Jed0vcela/LabSupply-2025-2026/3D files/button handle tapered hole V2 NO_AMS.SLDPRT

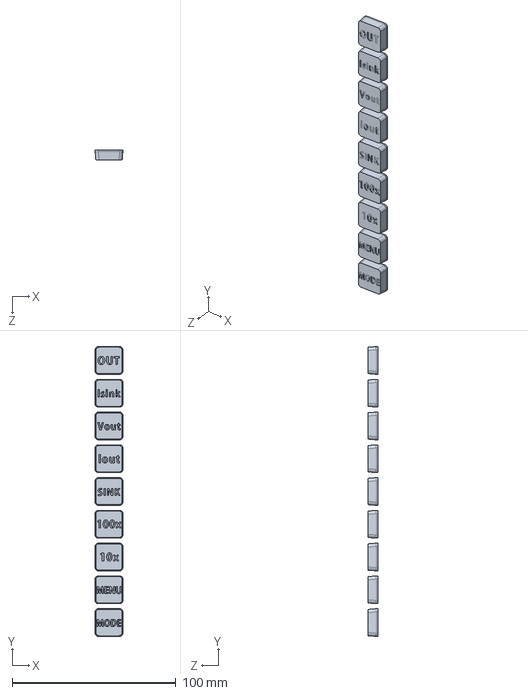
[picture p5: CAD file, 2026-05-19]
3D files/button handle tapered hole V2 NO_AMS.SLDPRT
17.0 x 177.0 x 6.00 mm
