Jed0vcela/LabSupply-2025-2026/3D files/STLs/button handle v2.STL

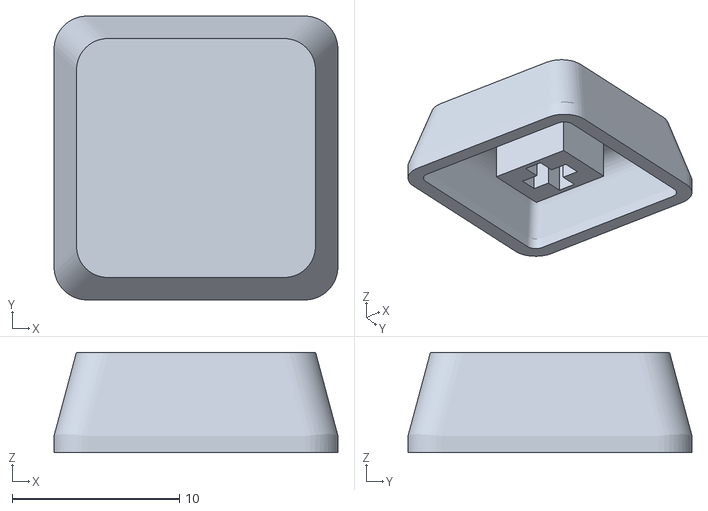
[picture p7: CAD file, 2026-05-17]
3D files/STLs/button handle v2.STL
17.0 x 17.0 x 6.00
