Jed0vcela/LabSupply-2025-2026/3D files/button handle tapered hole V2 AMS.SLDPRT

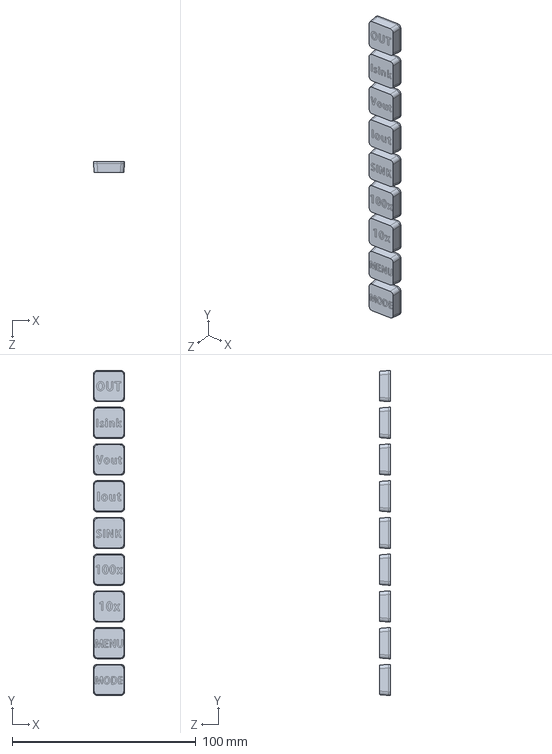
[picture p8: CAD file, 2026-05-18]
3D files/button handle tapered hole V2 AMS.SLDPRT
17.0 x 177.0 x 6.00 mm
