Jed0vcela/LabSupply-2025-2026/3D files/DXFc/FrontPanel1.DXF

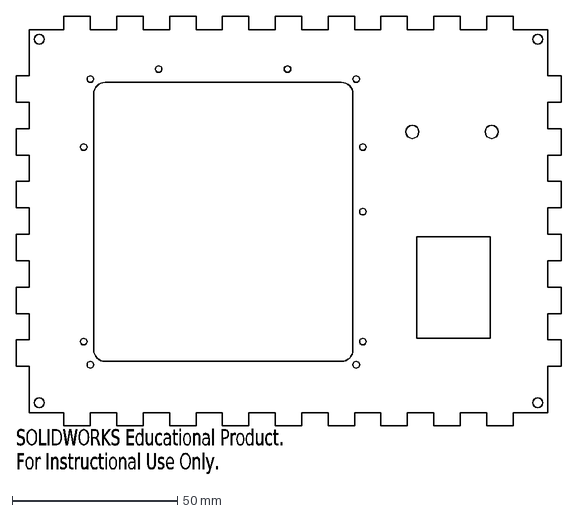
[picture p9: CAD file, 2026-05-18]
3D files/DXFc/FrontPanel1.DXF
SOLIDWORKS Educational Product.
For Instructional Use Only.
