Jed0vcela/LabSupply-2025-2026/3D files/STLs/front panel cover^supply_assem.STL

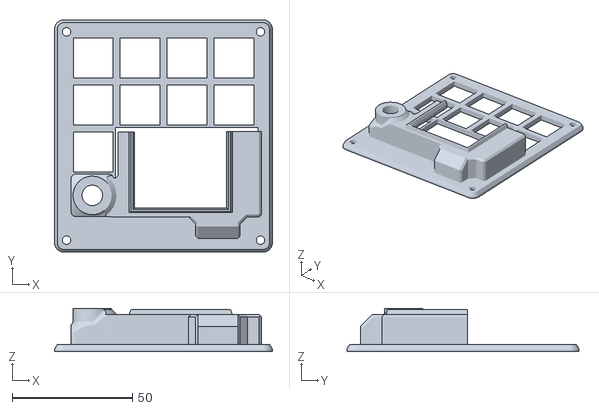
[picture p10: CAD file, 2026-05-17]
3D files/STLs/front panel cover^supply_assem.STL
90.5 x 96.5 x 18.0
