Jed0vcela/LabSupply-2025-2026/3D files/DXFc/RightPanel1.DXF

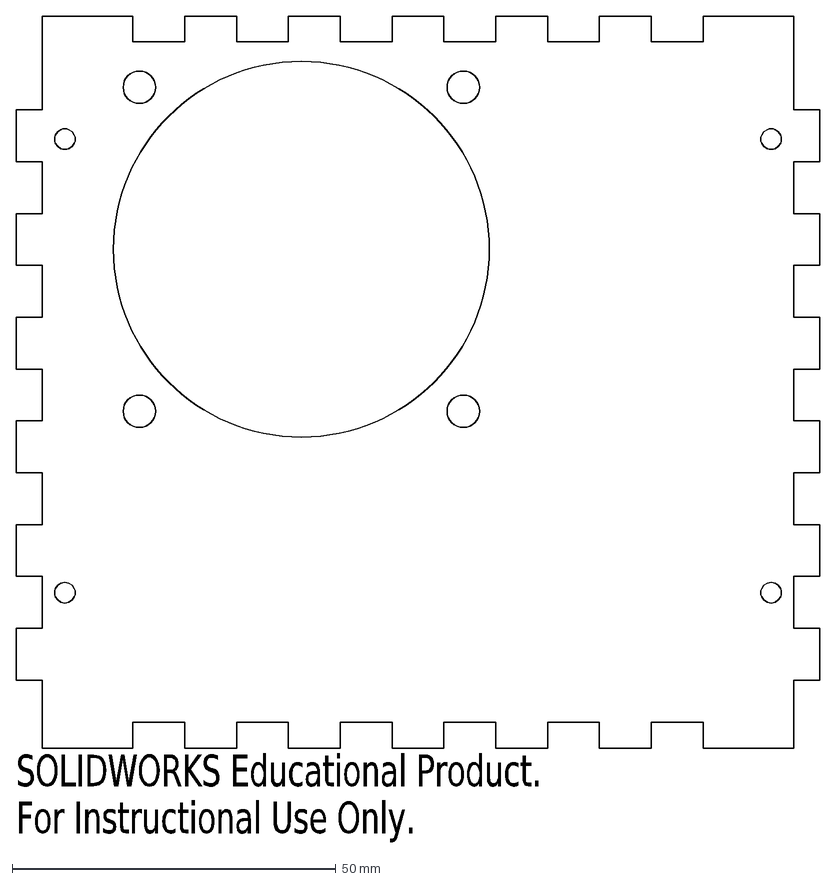
[picture p11: CAD file, 2026-05-18]
3D files/DXFc/RightPanel1.DXF
SOLIDWORKS Educational Product.
For Instructional Use Only.
