Jed0vcela/LabSupply-2025-2026/3D files/FrontPanel1.SLDPRT

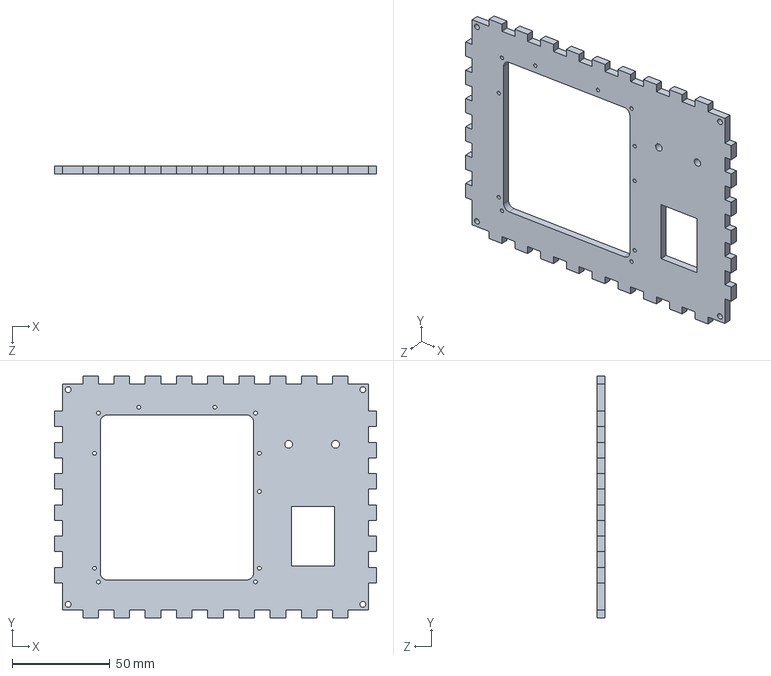
[picture p12: CAD file, 2026-05-18]
3D files/FrontPanel1.SLDPRT
165.0 x 124.0 x 4.00 mm
