Jed0vcela/LabSupply-2025-2026/3D files/PwrBrd/single-banana-jack-1.snapshot.2/Banana Jack/baseplate.SLDPRT

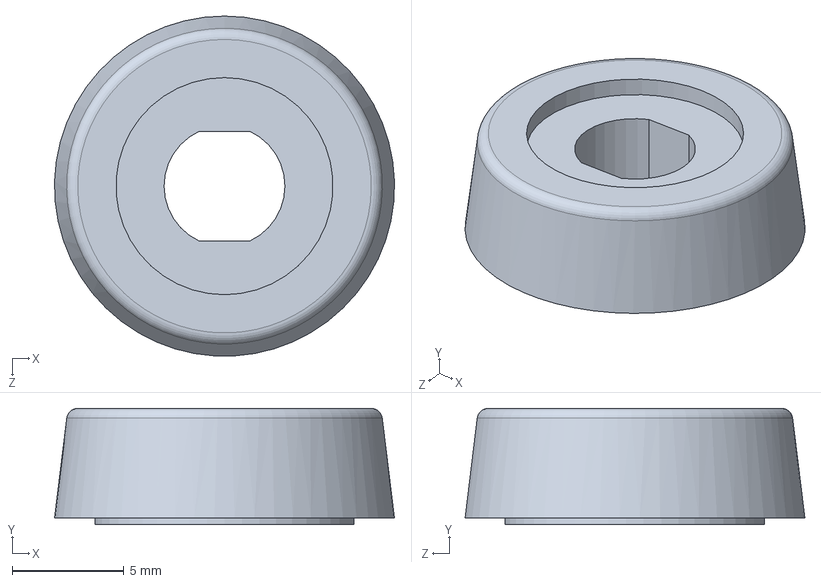
[picture p13: CAD file, 2026-05-11]
3D files/PwrBrd/single-banana-jack-1.snapshot.2/Banana Jack/baseplate.SLDPRT
15.2 x 5.20 x 15.2 mm
