Jed0vcela/LabSupply-2025-2026/3D files/STLs/front panel mount rear^supply_assem.STL

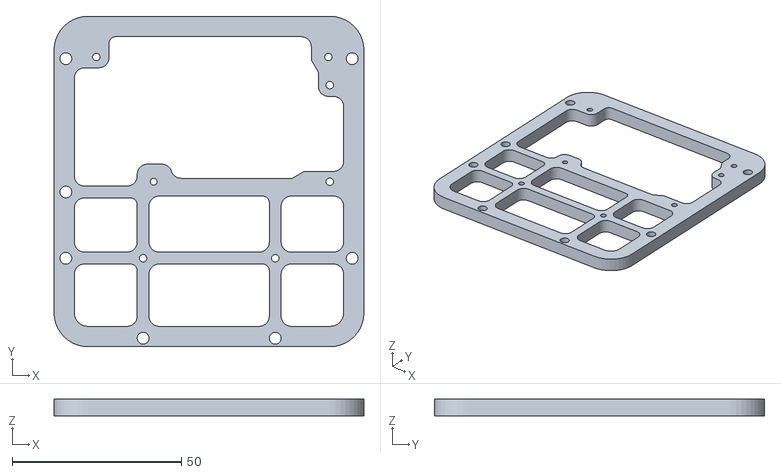
[picture p14: CAD file, 2026-05-16]
3D files/STLs/front panel mount rear^supply_assem.STL
91.5 x 97.5 x 5.00
