Jed0vcela/LabSupply-2025-2026/3D files/DXFc/Copy of TopPanel1^supply_assem.DXF

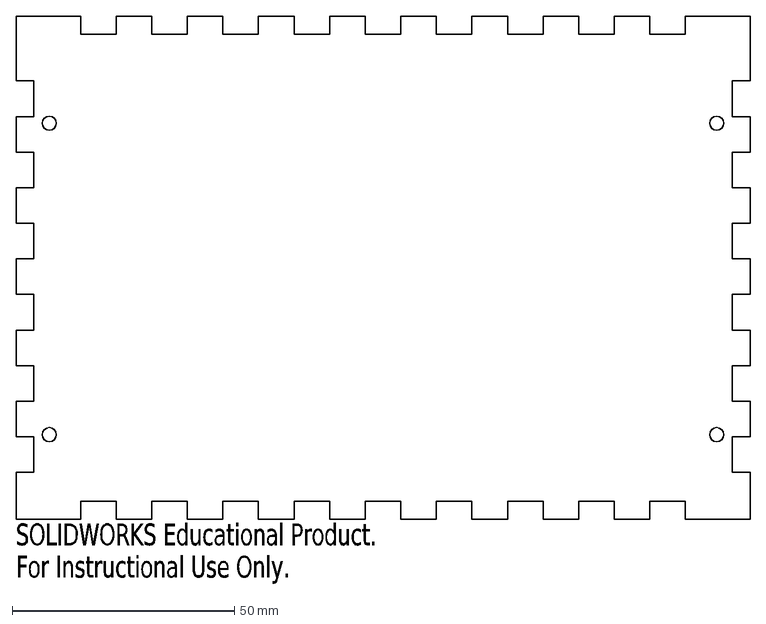
[picture p15: CAD file, 2026-05-18]
3D files/DXFc/Copy of TopPanel1^supply_assem.DXF
SOLIDWORKS Educational Product.
For Instructional Use Only.
