Jed0vcela/LabSupply-2025-2026/3D files/Fuse Holder 5x20mm v1.SLDPRT

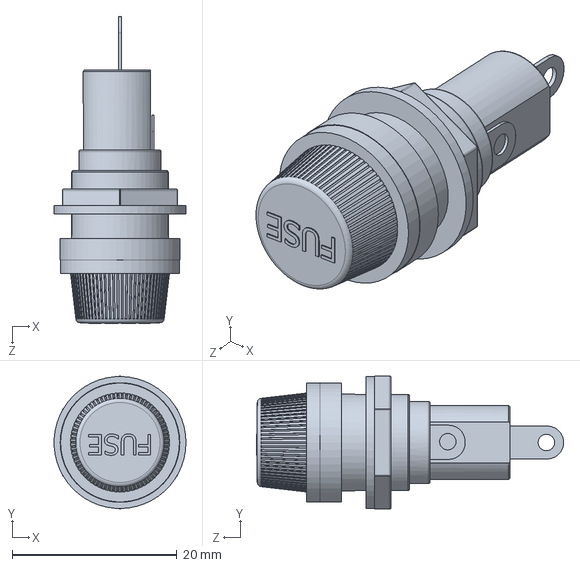
[picture p16: CAD file, 2026-05-18]
3D files/Fuse Holder 5x20mm v1.SLDPRT
16.0 x 16.1 x 37.2 mm
