Jed0vcela/LabSupply-2025-2026/3D files/STLs/drill guide^supply_assem.STL

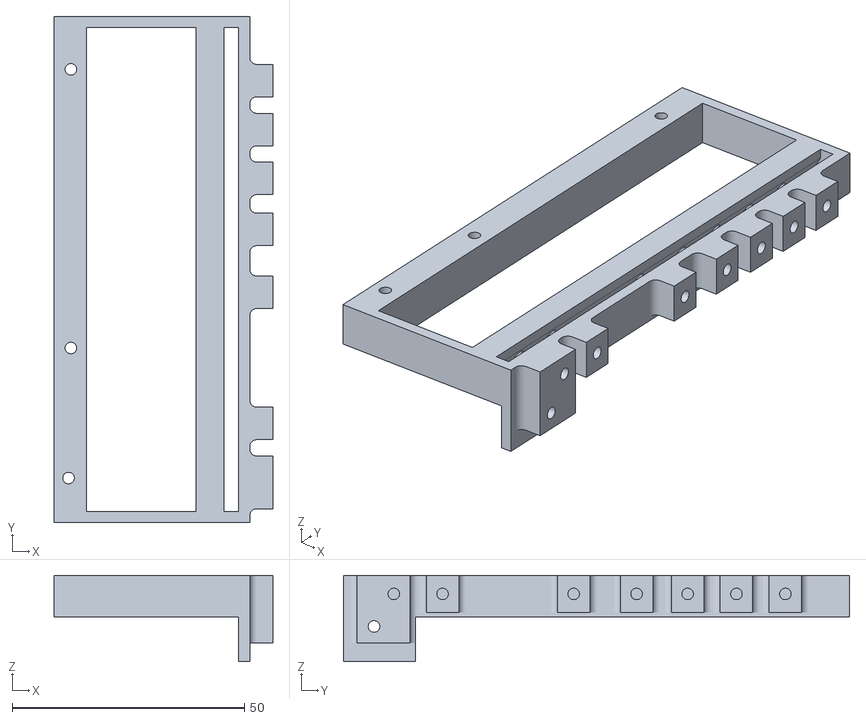
[picture p17: CAD file, 2026-05-11]
3D files/STLs/drill guide^supply_assem.STL
47.2 x 109.0 x 18.6
