Jed0vcela/LabSupply-2025-2026/3D files/STLs/USB-C PD trigger holder^supply_assem.STL

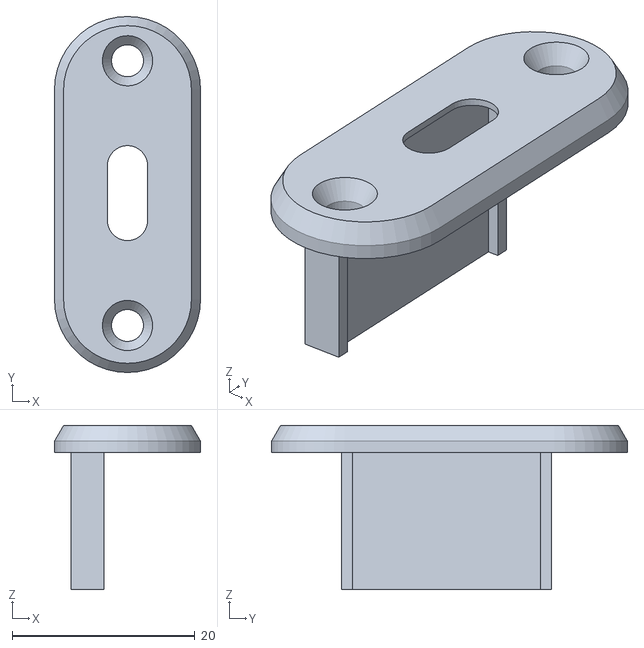
[picture p19: CAD file, 2026-05-11]
3D files/STLs/USB-C PD trigger holder^supply_assem.STL
16.0 x 39.0 x 18.0
