Jed0vcela/LabSupply-2025-2026/3D files/DXFc/BottomPanel1.DXF

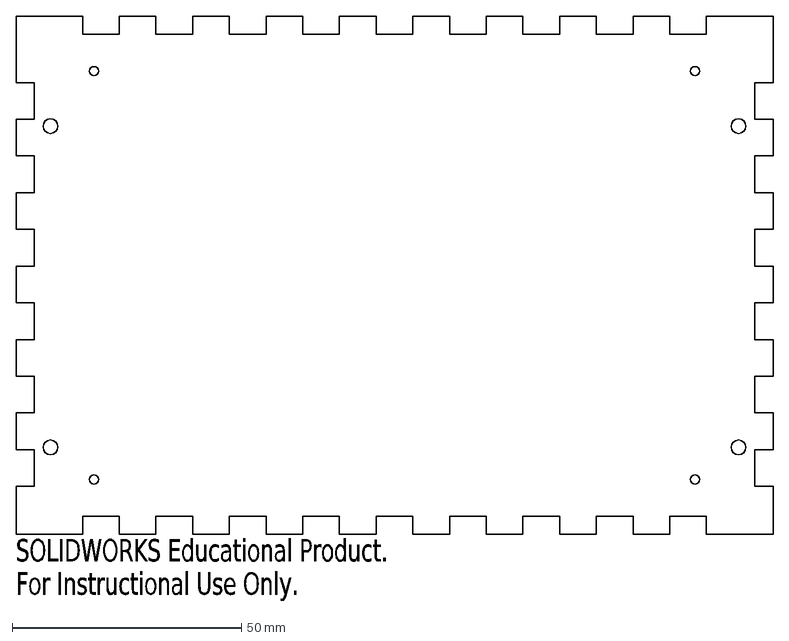
[picture p20: CAD file, 2026-05-18]
3D files/DXFc/BottomPanel1.DXF
SOLIDWORKS Educational Product.
For Instructional Use Only.
