Jed0vcela/LabSupply-2025-2026/3D files/knob1.SLDPRT

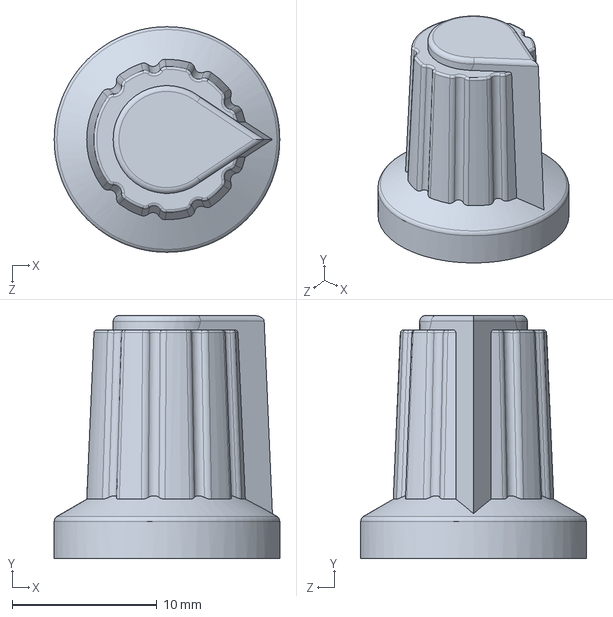
[picture p21: CAD file, 2026-05-18]
3D files/knob1.SLDPRT
15.6 x 16.8 x 15.6 mm
