Jed0vcela/LabSupply-2025-2026/3D files/STLs/fan side holder^supply_assem.STL

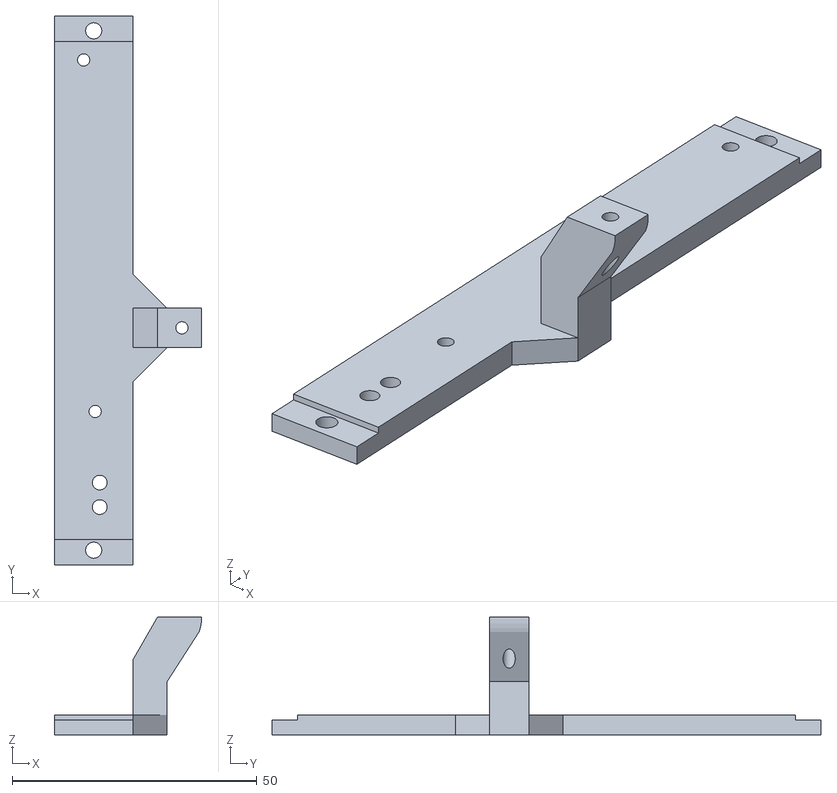
[picture p22: CAD file, 2026-05-11]
3D files/STLs/fan side holder^supply_assem.STL
30.0 x 112.0 x 24.0
