Jed0vcela/LabSupply-2025-2026/3D files/DXFc/frame^supply_assem.STL

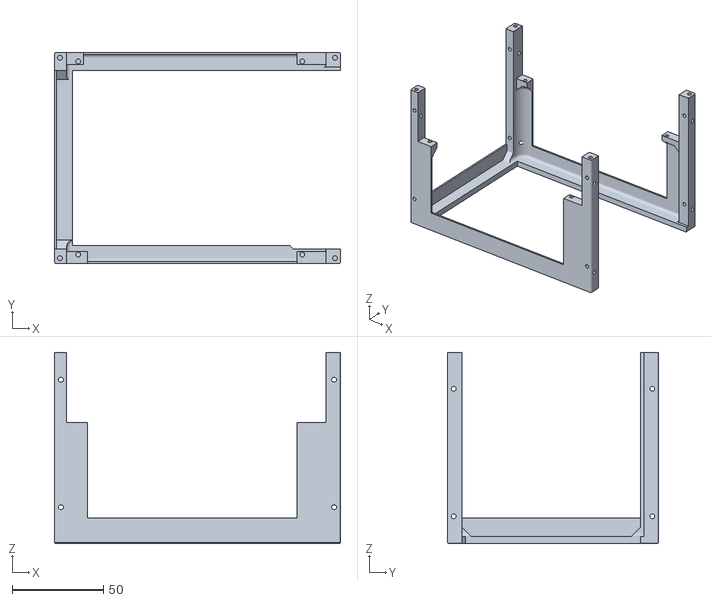
[picture p23: CAD file, 2026-05-11]
3D files/DXFc/frame^supply_assem.STL
157.0 x 116.0 x 105.0
