Jed0vcela/LabSupply-2025-2026/3D files/LeftPanel1.SLDPRT

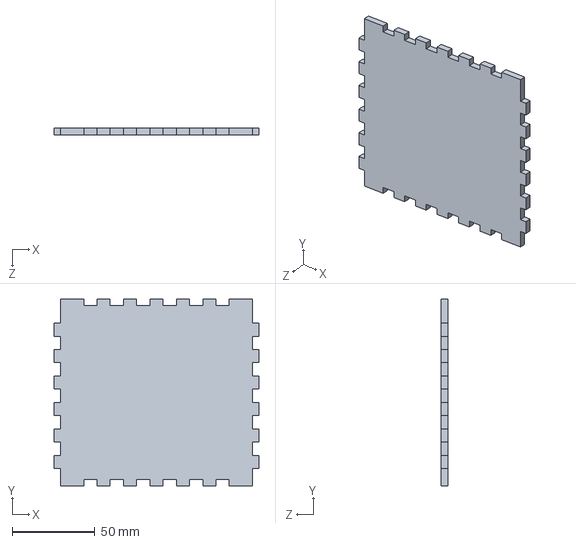
[picture p24: CAD file, 2026-05-18]
3D files/LeftPanel1.SLDPRT
124.0 x 113.0 x 4.00 mm
