Jed0vcela/LabSupply-2025-2026/3D files/PwrBrd/single-banana-jack-1.snapshot.2/Banana Jack/baseplate_1.SLDPRT

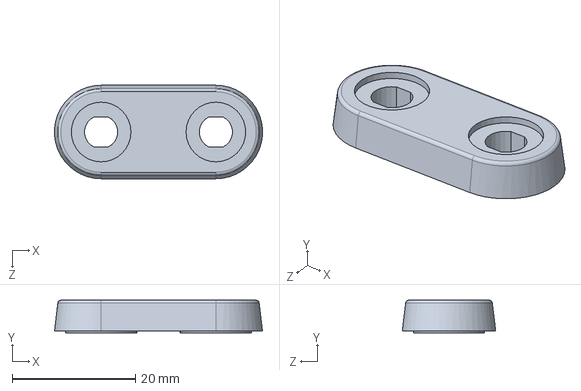
[picture p25: CAD file, 2026-05-11]
3D files/PwrBrd/single-banana-jack-1.snapshot.2/Banana Jack/baseplate_1.SLDPRT
33.8 x 5.30 x 15.2 mm
