Jed0vcela/LabSupply-2025-2026/3D files/STLs/USB cover^supply_assem.STL

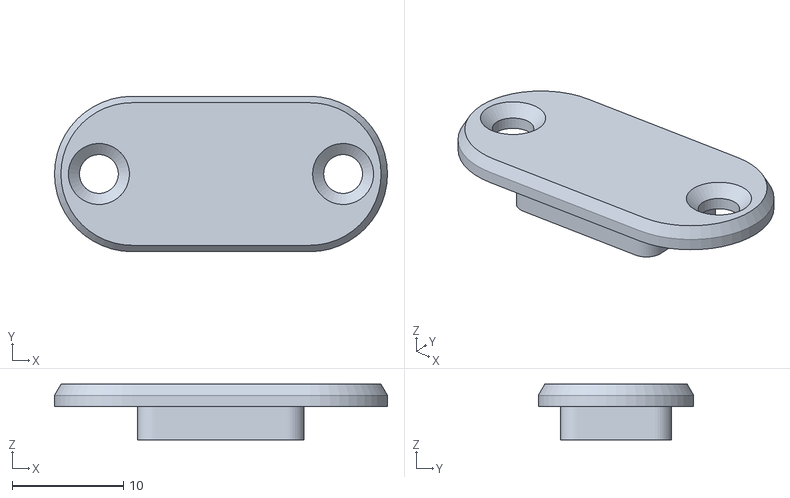
[picture p26: CAD file, 2026-05-11]
3D files/STLs/USB cover^supply_assem.STL
30.0 x 14.0 x 5.00
