Jed0vcela/LabSupply-2025-2026/3D files/STLs/inductor side holder^supply_assem.STL

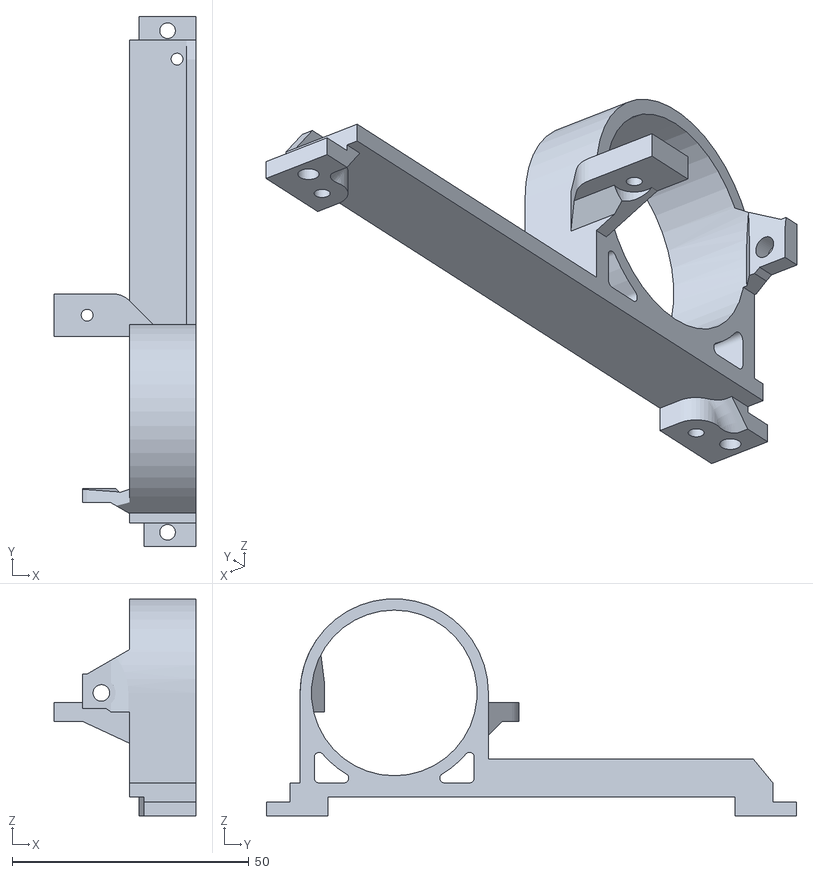
[picture p27: CAD file, 2026-05-11]
3D files/STLs/inductor side holder^supply_assem.STL
30.0 x 112.0 x 45.8
