Jed0vcela/LabSupply-2025-2026/3D files/panel XT60IE-M.SLDPRT

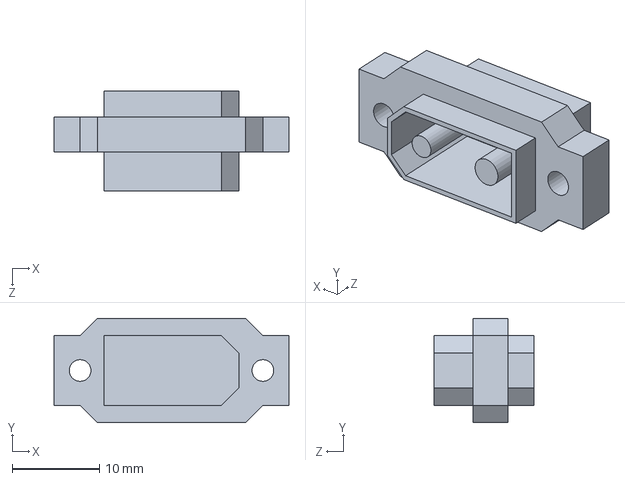
[picture p28: CAD file, 2026-05-11]
3D files/panel XT60IE-M.SLDPRT
27.0 x 12.0 x 11.5 mm
