Jed0vcela/LabSupply-2025-2026/3D files/PwrBrd/single-banana-jack-1.snapshot.2/Banana Jack/contact pin.sldprt

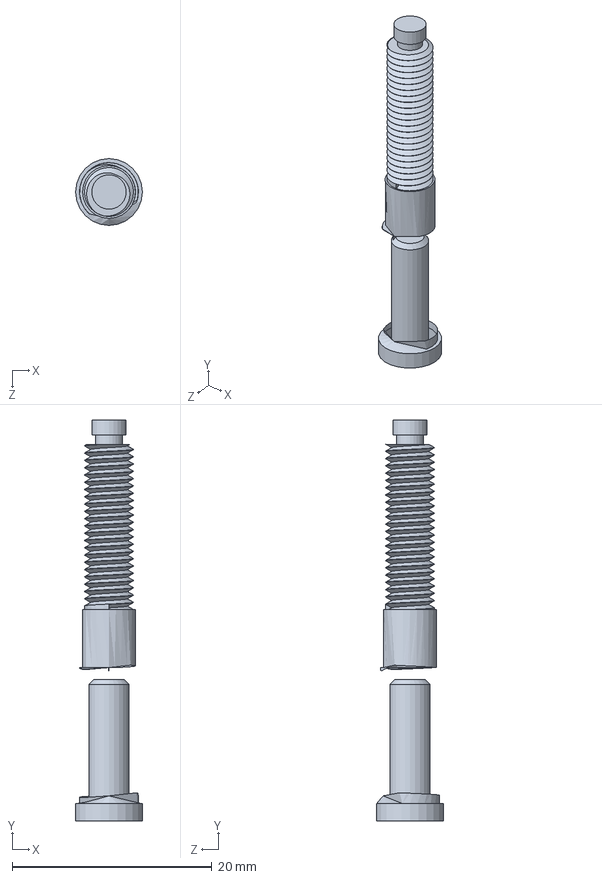
[picture p29: CAD file, 2026-05-11]
3D files/PwrBrd/single-banana-jack-1.snapshot.2/Banana Jack/contact pin.sldprt
6.70 x 40.2 x 6.70 mm
