Jed0vcela/LabSupply-2025-2026/3D files/TopPanel1.SLDPRT

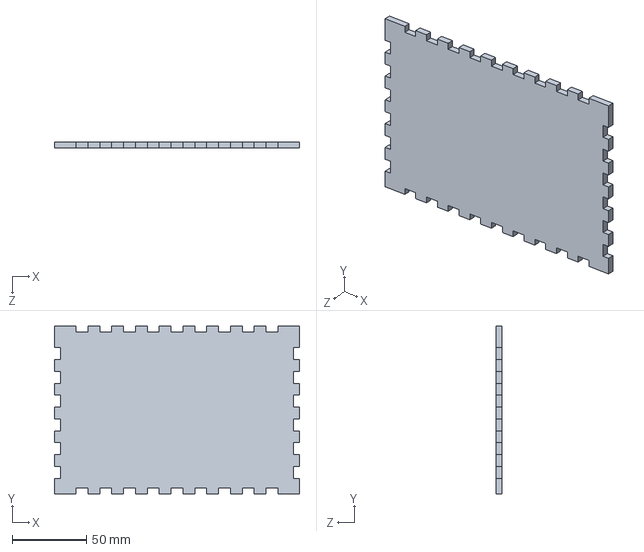
[picture p30: CAD file, 2026-05-11]
3D files/TopPanel1.SLDPRT
165.0 x 113.0 x 4.00 mm
