Jed0vcela/LabSupply-2025-2026/3D files/60mm fan.SLDPRT

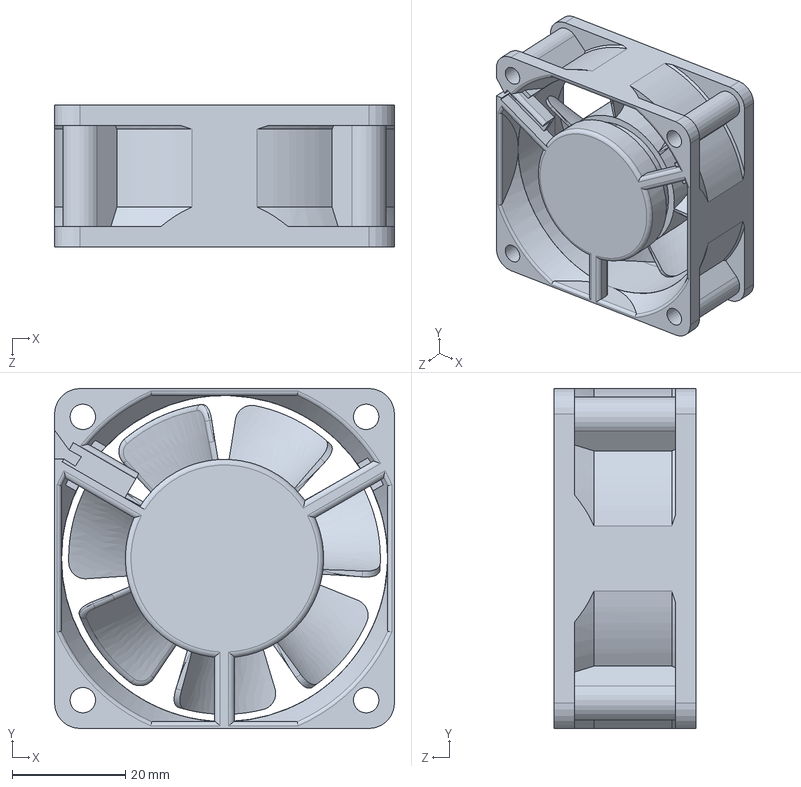
[picture p31: CAD file, 2026-05-11]
3D files/60mm fan.SLDPRT
60.0 x 60.0 x 25.0 mm
