Jed0vcela/LabSupply-2025-2026/3D files/big inductor.SLDPRT

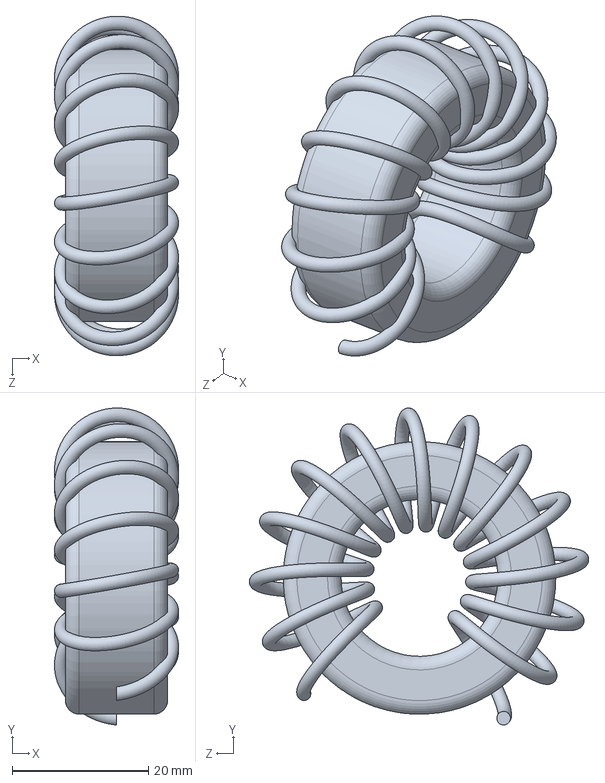
[picture p32: CAD file, 2026-05-11]
3D files/big inductor.SLDPRT
18.2 x 46.5 x 49.8 mm
