Jed0vcela/LabSupply-2025-2026/3D files/all wood boards.SLDPRT

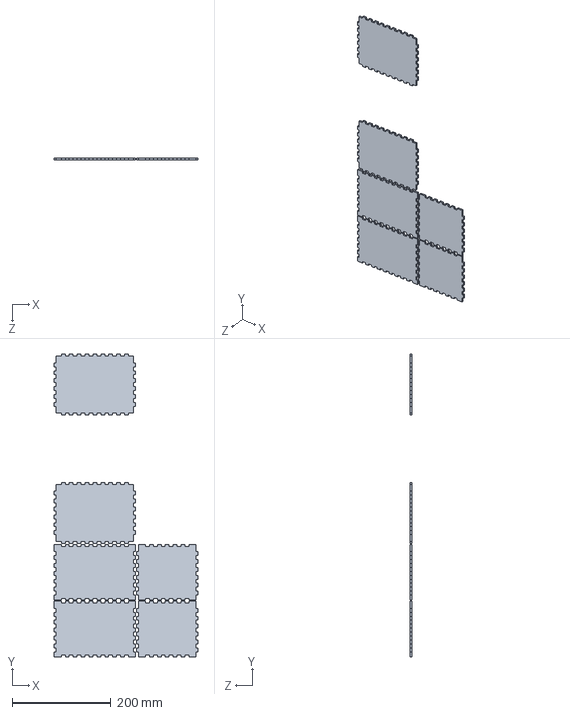
[picture p33: CAD file, 2026-05-11]
3D files/all wood boards.SLDPRT
291.0 x 614.0 x 4.00 mm
