Jed0vcela/LabSupply-2025-2026/3D files/100W 24V power supply.SLDPRT

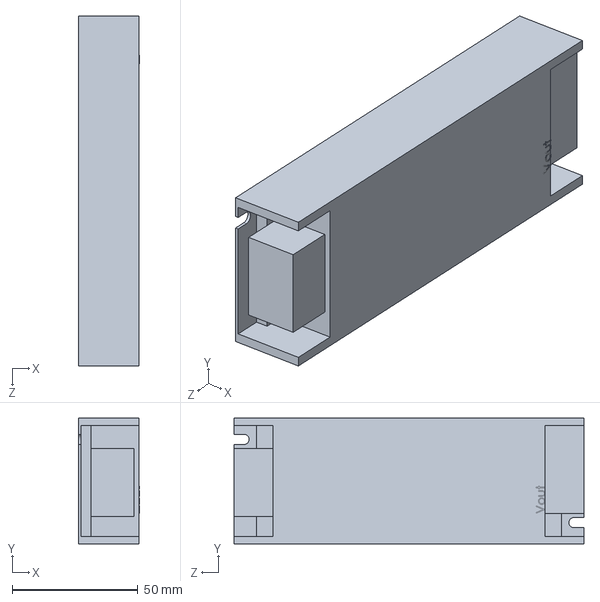
[picture p34: CAD file, 2026-05-11]
3D files/100W 24V power supply.SLDPRT
24.1 x 50.0 x 139.0 mm
