Jed0vcela/LabSupply-2025-2026/3D files/Power Switch R59-5BRBT2-G.SLDPRT

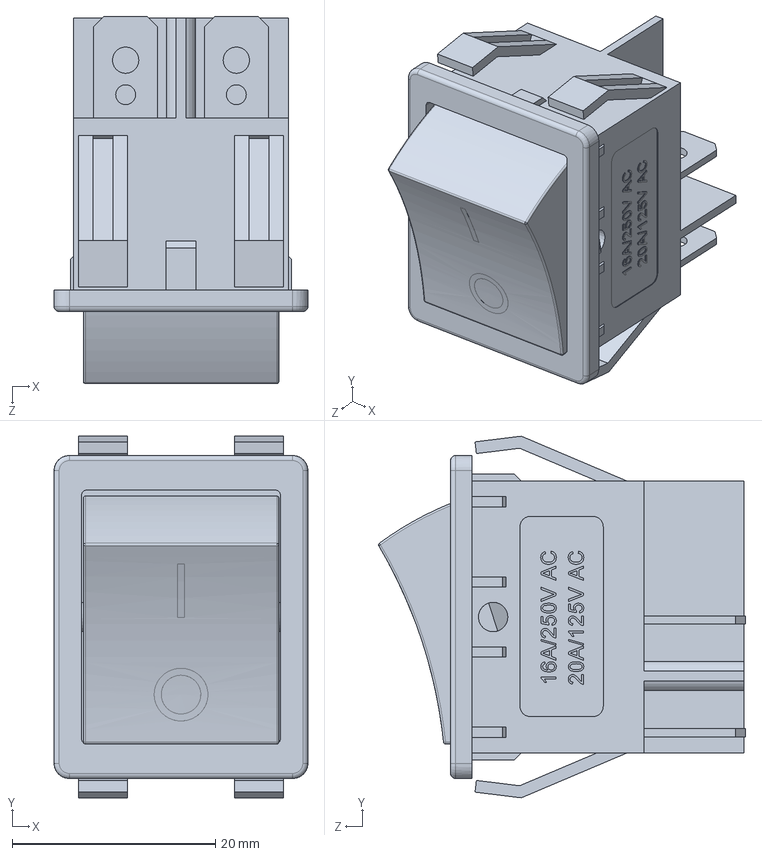
[picture p35: CAD file, 2026-05-11]
3D files/Power Switch R59-5BRBT2-G.SLDPRT
25.0 x 35.6 x 36.1 mm
