Jed0vcela/LabSupply-2025-2026/3D files/heatsink Al ZH0137 115x64x100mm.SLDPRT

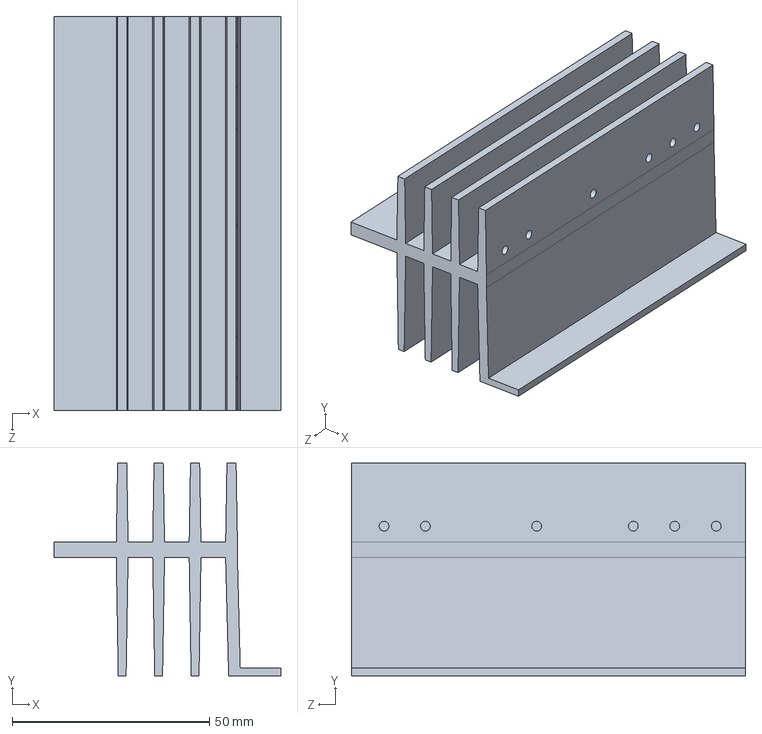
[picture p36: CAD file, 2026-05-11]
3D files/heatsink Al ZH0137 115x64x100mm.SLDPRT
57.5 x 54.0 x 100.0 mm
