Jed0vcela/LabSupply-2025-2026/3D files/USB-C PD trigger board.SLDPRT

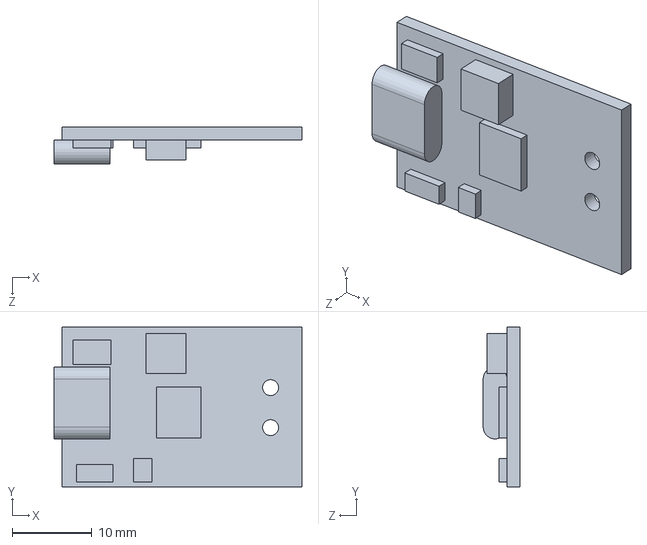
[picture p37: CAD file, 2026-05-11]
3D files/USB-C PD trigger board.SLDPRT
31.0 x 20.0 x 4.60 mm
