Jed0vcela/LabSupply-2025-2026/3D files/cherry mx buttons soldering guide v1.SLDPRT

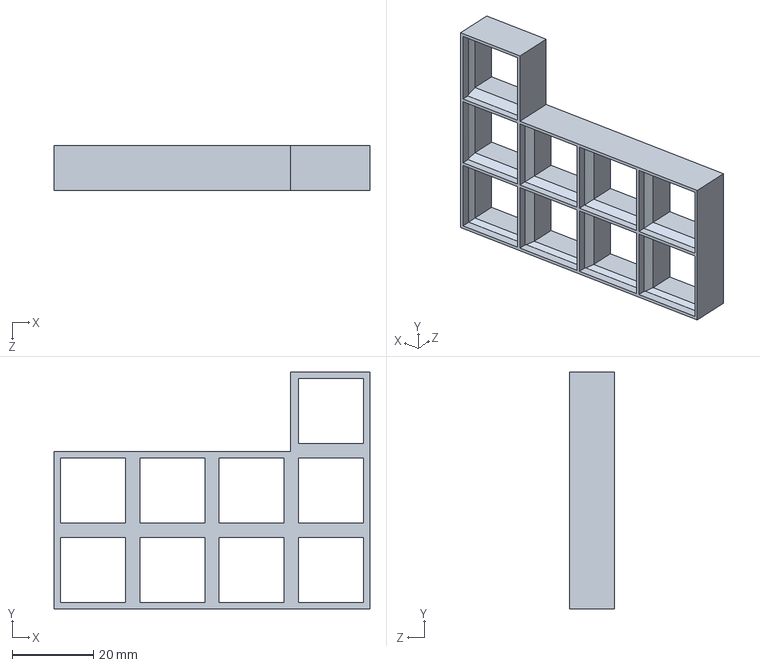
[picture p38: CAD file, 2026-05-11]
3D files/cherry mx buttons soldering guide v1.SLDPRT
77.7 x 58.2 x 11.0 mm
