Jed0vcela/LabSupply-2025-2026/3D files/BackPanel1.SLDPRT

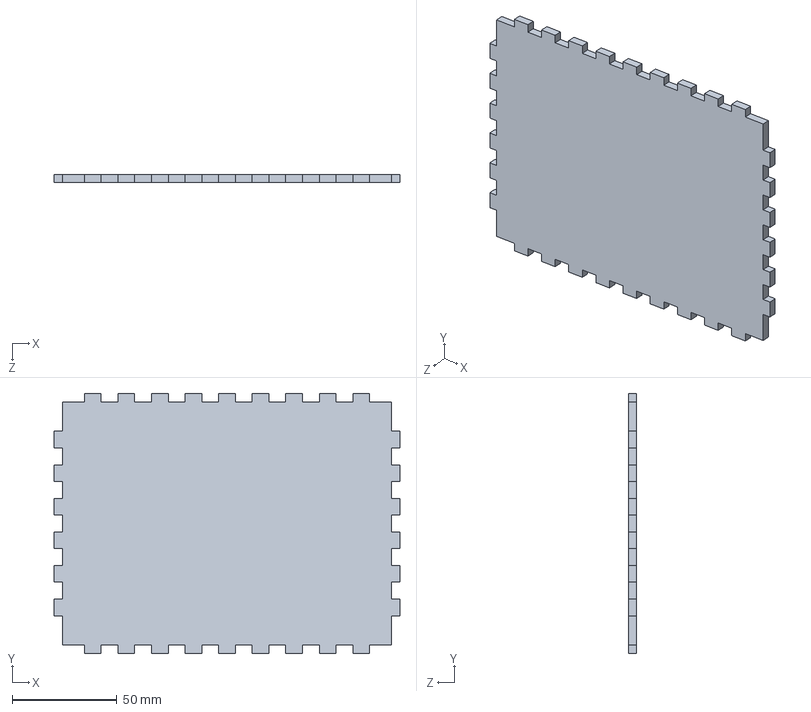
[picture p39: CAD file, 2026-05-11]
3D files/BackPanel1.SLDPRT
165.0 x 124.0 x 4.00 mm
