Jed0vcela/LabSupply-2025-2026/3D files/controlBrd/EC12E20-24P24C-SW.stp

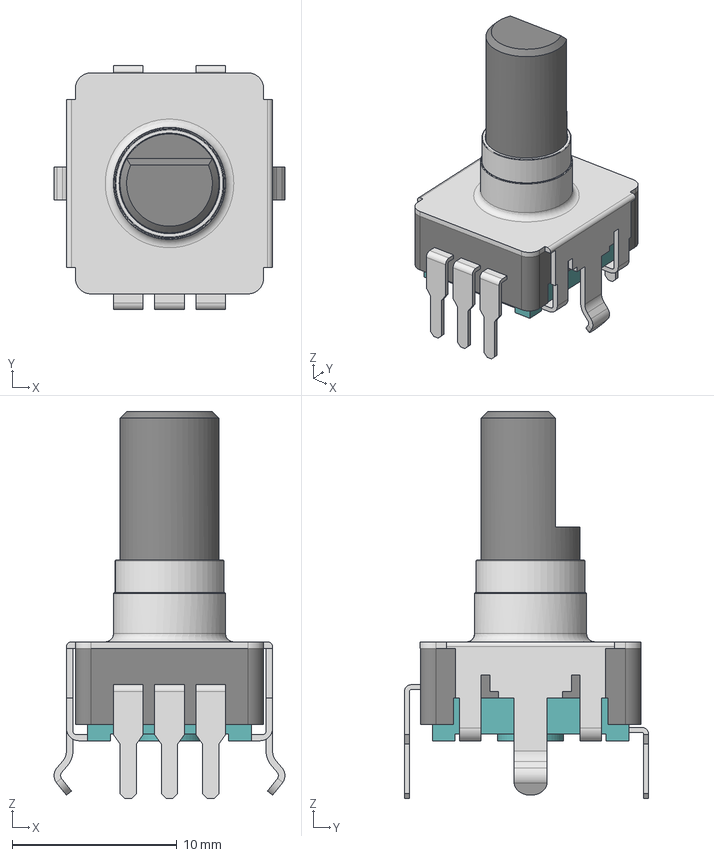
[picture p40: CAD file, 2026-05-11]
3D files/controlBrd/EC12E20-24P24C-SW.stp
14.0 x 14.8 x 23.5 mm
