Jed0vcela/LabSupply-2025-2026/3D files/Fan protection grill 55023 - 60mm X 60mm.SLDPRT

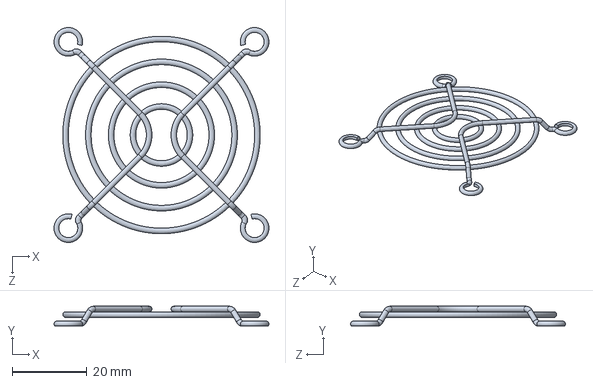
[picture p41: CAD file, 2026-05-11]
3D files/Fan protection grill 55023 - 60mm X 60mm.SLDPRT
57.7 x 5.25 x 57.7 mm
