Jed0vcela/LabSupply-2025-2026/3D files/iec320_703W-00_04.SLDPRT

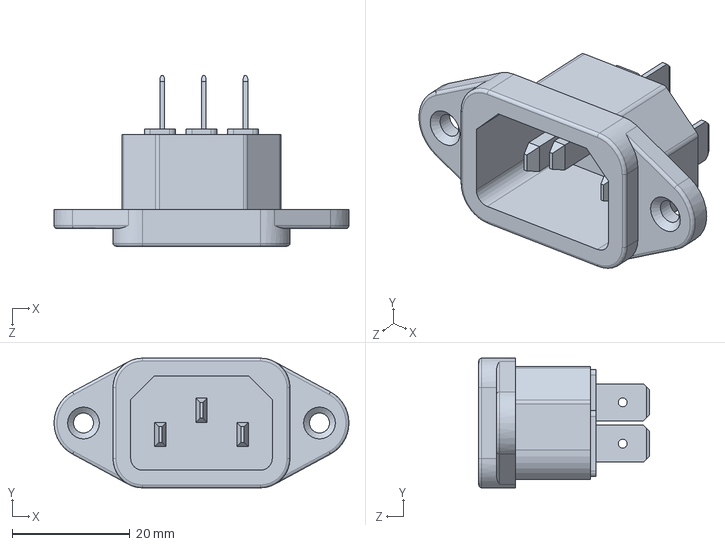
[picture p42: CAD file, 2026-05-11]
3D files/iec320_703W-00_04.SLDPRT
50.0 x 22.0 x 28.9 mm
