Jed0vcela/LabSupply-2025-2026/3D files/controlBrd/Cherry MX.STEP

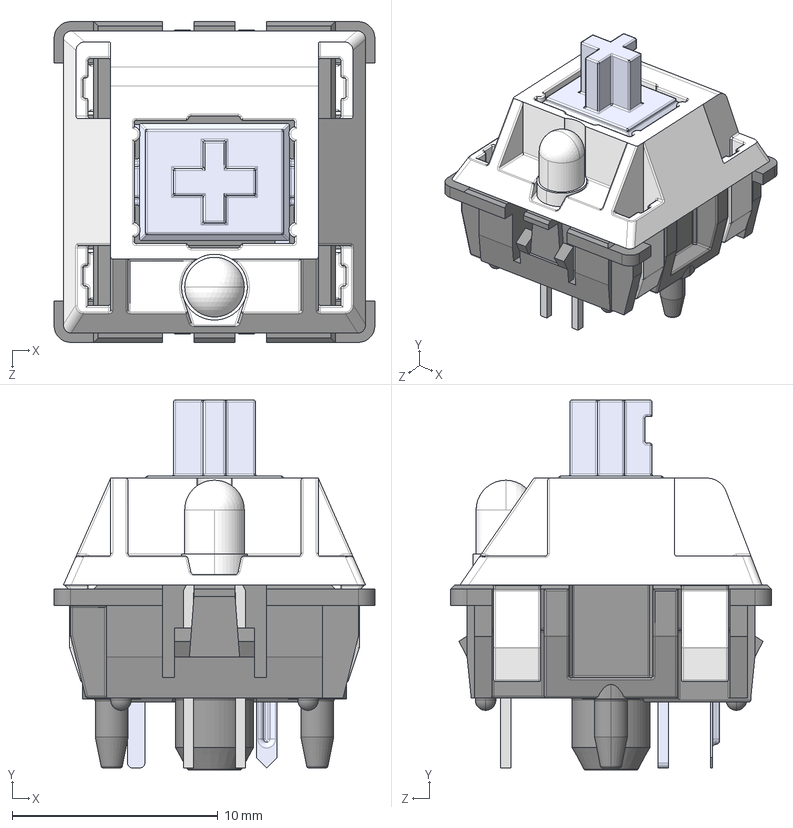
[picture p43: CAD file, 2026-05-11]
3D files/controlBrd/Cherry MX.STEP
15.6 x 18.0 x 15.6 mm
Bottom
Pulsador
Top
Pieza5^Cherry MX
Pin1
Pin2
Led 3mm_trans
