Jed0vcela/LabSupply-2025-2026/3D files/PwrBrd/LabSupply 2025-2026.SLDASM

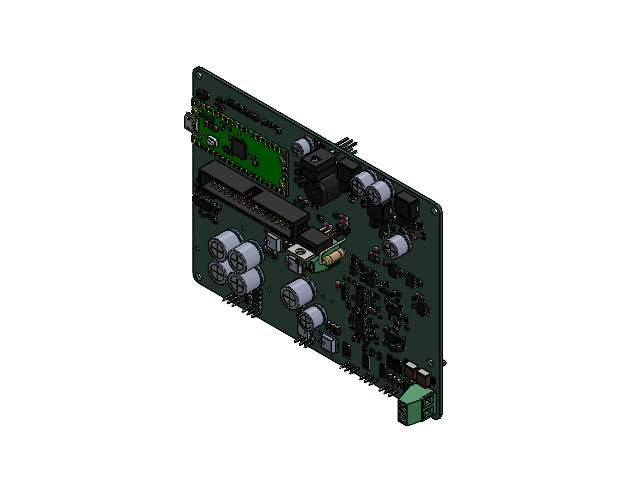
[picture p48: CAD file, 2026-05-11]
3D files/PwrBrd/LabSupply 2025-2026.SLDASM
LabSupply 2025-2026 1.46.1
LabSupply 2025-2026 1.56.1 x 3
PCB, Raspberry Pi Pico-R3
MicroUSB Port, Raspberry Pi Pico-R3
RP2040 Microcontroller, Raspberry Pi Pico-R3
SW1, Tact Switch, Raspberry Pi Pico-R3
D1, Diode, Schottky, Raspberry Pi Pico-R3
D2, QSME-C194, LED, Raspberry Pi Pico-R3
L1, Inductor, Raspberry Pi Pico-R3
U2, RT6150B-33GQW, Buck Boost Converter, Raspberry Pi Pico-R3
U3, W25Q16JVUXIQ, Serial NOR Flash 16 Mbit, Raspberry Pi Pico-R3
Q1, MOSFET, DMG1012T, Raspberry Pi Pico-R3
X1, X12M000000S096, 12 Mhz Crystal Resonator, Raspberry Pi Pico-R3
SMD Resistor, Configurable, Raspberry Pi Pico-R3_R1
SMD Resistor, Configurable, Raspberry Pi Pico-R3_R2
SMD Resistor, Configurable, Raspberry Pi Pico-R3_R3
SMD Resistor, Configurable, Raspberry Pi Pico-R3_R4
SMD Resistor, Configurable, Raspberry Pi Pico-R3_R5
SMD Resistor, Configurable, Raspberry Pi Pico-R3_R6
SMD Resistor, Configurable, Raspberry Pi Pico-R3_R7
SMD Resistor, Configurable, Raspberry Pi Pico-R3_R8
SMD Resistor, Configurable, Raspberry Pi Pico-R3_R9
SMD Resistor, Configurable, Raspberry Pi Pico-R3_R10
SMD Resistor, Configurable, Raspberry Pi Pico-R3_R11
SMD Resistor, Configurable, Raspberry Pi Pico-R3_R12
SMD Resistor, Configurable, Raspberry Pi Pico-R3_R13
SMD Resistor, Configurable, Raspberry Pi Pico-R3_R14
SMD Resistor, Configurable, Raspberry Pi Pico-R3_R15
SMD Capacitor, Configurable, Raspberry Pi Pico-R3_C1
SMD Capacitor, Configurable, Raspberry Pi Pico-R3_C2
SMD Capacitor, Configurable, Raspberry Pi Pico-R3_C3
SMD Capacitor, Configurable, Raspberry Pi Pico-R3_C4
SMD Capacitor, Configurable, Raspberry Pi Pico-R3_C5
SMD Capacitor, Configurable, Raspberry Pi Pico-R3_C6
SMD Capacitor, Configurable, Raspberry Pi Pico-R3_C7
SMD Capacitor, Configurable, Raspberry Pi Pico-R3_C8
SMD Capacitor, Configurable, Raspberry Pi Pico-R3_C9
SMD Capacitor, Configurable, Raspberry Pi Pico-R3_C10
SMD Capacitor, Configurable, Raspberry Pi Pico-R3_C11
SMD Capacitor, Configurable, Raspberry Pi Pico-R3_C12
SMD Capacitor, Configurable, Raspberry Pi Pico-R3_C13
SMD Capacitor, Configurable, Raspberry Pi Pico-R3_C14
SMD Capacitor, Configurable, Raspberry Pi Pico-R3_C15
SMD Capacitor, Configurable, Raspberry Pi Pico-R3_C16
SMD Capacitor, Configurable, Raspberry Pi Pico-R3_C17
SMD Capacitor, Configurable, Raspberry Pi Pico-R3_C18
Buzzer_12x9.5RM7.6
SOIC-8_3.9x4.9mm_P1.27mm x 9
MSOP-10_3x3mm_P0.5mm
CP_Radial_D10.0mm_P5.00mm x 5
R_0805_2012Metric x 97
D_MiniMELF x 5
SOT-23-6 x 7
TO-220-3_Vertical x 7
C_1206_3216Metric x 36
SOT-23 x 12
D_SMA x 4
D_SOD-123 x 7
C_0805_2012Metric x 43
TerminalBlock_Phoenix_MKDS-1,5-2_1x02_P5.00mm_Horizontal x 2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
